AtomicRoland/ElkWiFi/rom/flash.asm

\ Flash routine to reprogram the EEPROM.
\ (c) 2020 Roland Leurs
\ Version 1.0 14-08-2020
\
\ This code will be included in the EEPROM but is copied to the main memory before it is executed. You can copy it
\ by executing the WiFi driver function &FE where the Y register contains the high byte of the data to be "burned"
\ into the EEPROM and the A register contains the bank number within the EEPROM. Always the full 16kB will be "burned".
\
\ Bank 0:   &0000 - &3FFF       mfa = 1     bank = 0
\ Bank 1:   &4000 - &7FFF       mfa = 1     bank = 1
\ Bank 2:   &8000 - &BFFF       mfa = 0     bank = 0
\ Bank 3:   &C000 - &FFFF       mfa = 0     bank = 1
\ 
\ After the programming has finished the Electron will be hard reset because one of the ROMs will have changed and
\ the operating system needs to be reinitialized. Luckily, a reboot on the Electron does not take as much time as
\ rebooting a PC ;-)

\ Workspace
include "electron.asm"
mfatable  = zp+8                \ 4 bytes
banktable = zp+12               \ 4 bytes
src       = zp+16               \ 2 bytes
dst       = zp+18               \ 2 bytes

\ UART registers
uart_thr = uart+8
uart_dll = uart+8
uart_dlm = uart+9
uart_afr = uart+10
uart_lcr = uart+11
uart_mcr = uart+12


            org flashcode
\ Start with saving the A and Y registers. Versions up to (and including V0.30) called this routine with
\ the bank number in X. For TI16C2552 support it is more convinient to use A.
.flash      sta save_x          \ save bank number in the EEPROM
            sty save_y          \ save start address of data
            sei                 \ no more interrupts from here

\ Start with setting up the UART A-port for controlling the MFA pin (A15 of the EEPROM)
            lda uart_lcr        \ enable MFR register
            ora #&80
            sta uart_lcr
            lda #&01            \ set divisor to 1. 115k2
            sta uart_dll
            lda #&00
            sta uart_dlm
            sta uart_afr        \ set MFA to output
            lda #&03            \ 8 bit, 1 stop, no parity
            sta uart_lcr

\ First build a table with values for the MBA bit and bank numbers
            lda #&08            \ MFA bit set for bank 0 and bank 1
            sta mfatable
            sta mfatable+1
            lda #&00            \ MFA bit cleared for bank 2 and bank 3
            sta mfatable+2
            sta mfatable+3
            lda &F4             \ load current paged rom number
            and #&06            \ clear lowest bit
            tay                 \ move to Y for odd bank numbers
            sty banktable
            sty banktable+2
            iny                 \ increment Y register for even bank numbers
            sty banktable+1
            sty banktable+3
 
\ Blank the bank (bank number is in X register)
            lda #'E'            \ print the E(rase)
            jsr print
            jsr prepare_erase   \ prepare the erase operation
            sta &8000           \ erase first sector
            jsr wait            \ wait for completion
            lda #'*'            \ print a * as progress indicator
            jsr oswrch
            jsr prepare_erase   \ prepare the erase operation
            sta &9000           \ erase second sector
            jsr wait            \ wait for completion
            lda #'*'            \ print a * as progress indicator
            jsr oswrch
            jsr prepare_erase   \ prepare the erase operation
            sta &A000           \ erase third sector
            jsr wait            \ wait for completion
            lda #'*'            \ print a * as progress indicator
            jsr oswrch
            jsr prepare_erase   \ prepare the erase operation
            sta &B000           \ erase fourth sector
            jsr wait            \ wait for completion
            lda #'*'            \ print a * as progress indicator
            jsr oswrch
            jsr osnewl          \ print a new line            

\ Program the bank
            lda #'P'            \ print the P(rogram)
            jsr print
            lda save_y          \ set source address in zero page
            sta src+1
            lda #&00
            sta src
            sta dst             \ set destination address in zero page
            lda #&80
            sta dst+1
            ldy #0              \ reset pointer
.prgloop1   jsr program         \ program the next byte
            iny                 \ increment pointer
            bne prgloop1        \ jump if 256 byte block not finished
            lda #'*'            \ print a * as progress indicator
            jsr oswrch
            inc src+1           \ increment source pointer (only MSB)
            inc dst+1           \ increment destination pointer (only MSB)
            lda dst+1           \ load destination pointer
            cmp #&C0            \ test if complete bank is programmed
            bne prgloop1        \ if not then continue with next block


\ End of routine                \ The first bytes are a copy of the original reset routine
.reset      LDA #&40
            STA &0D00
            SEI
            CLD
            LDX #&FF
            TXS
            INX
            STX &FE00
            STX &028D
            LDA #&F8
            STA &FE05           \ Until here it's a copy
            LDA &FFFC           \ might be mrb so calculate jmp address from reset vector
            CLC                 \ the offset is &19 in original and mrb OS's   (John W.)
            ADC #&19
            STA zp
            LDA &FFFD
            ADC #0
            STA zp+1
            LDA #2              \ This value is normally read from the ULA to check a power on reset
            JMP (zp)            \ Force a cold reset by continuing in the OS ROM
            
\ Prepare the erase operation for a sector in bank X. After returning from this subroutine
\ immediatly write to the sector address.
.prepare_erase
            lda #&AA            \ initialize the Sector-Erase command sequence
            jsr write5555
            lda #&55
            jsr write2AAA
            lda #&80
            jsr write5555
            lda #&AA
            jsr write5555
            lda #&55
            jsr write2AAA
            ldx save_x          \ reload bank number in X
            jsr setbank         \ set MFA and bank for the bank number in X
            lda #&30            \ start the erase operation
\            sta uart_thr
            rts                 \ ready with preparation

\ Write a byte to the EEPROM. The bank number should be in the X register, the
\ source is at (src),Y and the destination is at (dst),Y
.program    lda #&AA            \ Initialize the Byte-Program sequence
            jsr write5555
            lda #&55
            jsr write2AAA
\            sta uart_thr
            lda #&A0
            jsr write5555
            ldx save_x          \ reload bank number in X
            jsr setbank         \ select the bank to program (was changed by the writes above)
            lda (src),y         \ load source data
            sta (dst),y         \ write to destination
            jsr wait            \ wait for programming to complete
            rts                 \ return to calling routine

\ Wait until an operation has finished. I use the "toggle bit" method; this means that during the
\ erase or program operation bit 6 will be toggled at every read cycle.
.wait       lda &8000           \ load data
            and #&40            \ clear all bits except bit 6
.waitloop   sta zp+7            \ store in zero page
            lda &8000           \ load data
            and #&40            \ clear all bits except bit 6
            cmp zp+7            \ compare with previous read
            bne waitloop        \ continue with next wait cycle if they are not equal
.waitend    rts                 \ return to calling routine

\ Select the active bank for writing a byte to. The bank number is in the X register
.setbank    pha                 \ save A (it contains the byte that should be written)
            lda mfatable,x      \ load MFA value
            sta uart_mcr        \ write to UART (this sets A15 of the EEPROM)
            lda #&0F
            sta &FE05
            lda banktable,x     \ load sideway bank number
            sta &FE05           \ write to ULA
            pla                 \ restore A
            rts                 \ return to calling routine

\ Write a value to &5555 of the EEPROM (not the 6502 address!)
.write5555  ldx #1              \ &5555 is in bank 1
            jsr setbank         \ select bank 1
            sta &9555           \ write to the right address (this is the 6502 address in SWR space)
            ldx save_x          \ restore X register
            rts                 \ return to calling routine

\ Write a value to &2AAA of the EEPROM (not the 6502 address!)
.write2AAA  ldx #0              \ &2AAA is in bank 0
            jsr setbank         \ select bank 0
            sta &AAAA           \ write to the right address (this is the 6502 address in SWR space)
            ldx save_x          \ restore X register
            rts                 \ return to calling routine

\ Print the character in A, followed with a colon and a space.
.print      jsr oswrch          \ print the character in A
            lda #':'            \ load a colon
            jsr oswrch          \ print it
            lda #' '            \ load a space
            jmp oswrch          \ print it and return

.printhex           pha                     \ save accu
                    lsr a                   \ shift high nibble to low
                    lsr a
                    lsr a
                    lsr a
                    jsr printhex_l1         \ print nibble
                    pla                     \ restore value
 .printhex_l1       and #&0F                \ remove high nibble
                    cmp #&0A                \ test for hex digit
                    bcc printhex_l2         \ if not then continue
                    adc #6                  \ add 6 for hex letter
 .printhex_l2       adc #&30                \ add &30 for ascii value
                    jsr osasci              \ print the digit and return
                    rts

.flash_end

SAVE "flash.bin", flash, flash_end
