AtomicRoland/ElkWiFi/rom/wificmd.asm

\ Sideway ROM for Electron Wifi board
\ (c) Roland Leurs, May 2020

\ Wifi command
\ Version 1.00

\ Syntax: *WIFI [ON | OFF | SR | HR | R0 | R1]

.wifi_cmd       lda (line),y                \ load current character in command line
                cmp #&0D                    \ test if no paramaters given
                beq wifi_badcmd             \ if &0D then there are no parameters
                jsr skipspace               \ forward Y pointer to first non-space character
                and #&DF                    \ convert to upper case
                cmp #'O'                    \ It's on or off
                beq wifi_on_off
                cmp #'S'                    \ Soft reset
                beq wifi_sr                 
                cmp #'H'                    \ Hard reset
                beq wifi_hr
                cmp #'R'                    \ Select RAM bank
                beq wifi_rambank
.wifi_badcmd    jmp wifi_help               \ unrecognised or no parameter, print help text

.wifi_hr        ldx #1                      \ load driver command for hard reset (toggle RTS line)
                bne wifi_reset              \ branch always

.wifi_sr        ldx #0                      \ load driver command for soft reset (send AT+RST)
.wifi_reset     iny                         \ increment pointer to command line
                lda (line),y                \ load next character
                and #&DF                    \ convert to upper case
                cmp #'R'                    \ check if second letter is an R                
                bne wifi_badcmd             \ No it's not, go print help info
                txa                         \ transfer driver command to A
                jsr wifidriver              \ perform the action
                jmp call_claimed            \ end of command

.wifi_on_off    jsr skipspace               \ read the next character (skips space but that won't matter)
                and #&DF                    \ convert to upper case
                cmp #'N'                    \ it's an N, so wifi on
                beq wifi_on
                cmp #'F'                    \ if's an F, so wifi off
                bne wifi_badcmd             \ No F, so unrecognized command

.wifi_off       jsr printtext
                equs "Switching wifi off",&0D,&EA
                ldx #0                      \ switch wifi off (pass call to wifi driver)
.wifi_off_l1    lda #24
                jsr wifidriver              
                jmp call_claimed

.wifi_on        jsr printtext               \ for now this will do
                equs "Switching wifi on",&0D,&EA
                lda #1                      \ switch wifi on
                bne wifi_off_l1             \ branch always

.wifi_rambank   jsr skipspace               \ read the next character
                cmp #'0'                    \ Check for RAM bank 0
                beq wifi_rambank0
                cmp #'1'                    \ Check for RAM bank 1
                bne wifi_badcmd             \ Not '1' so it is an unrecognised value
                
.wifi_rambank1  jsr set_bank_1
                jmp call_claimed

.wifi_rambank0  jsr set_bank_0
                jmp call_claimed

.wifi_help      jsr printtext
                equs " ON   enable wifi",&0D
                equs " OFF  disable wifi",&0D
                equs " SR   perform soft reset",&0D
                equs " HR   perform hard reset",&0D
                equs " R0   select RAM bank 0",&0D
                equs " R1   select RAM bank 1",&0D,&EA
                jmp call_claimed
